peclik/ogn-airtracker/doc/img/battcharger.jpg

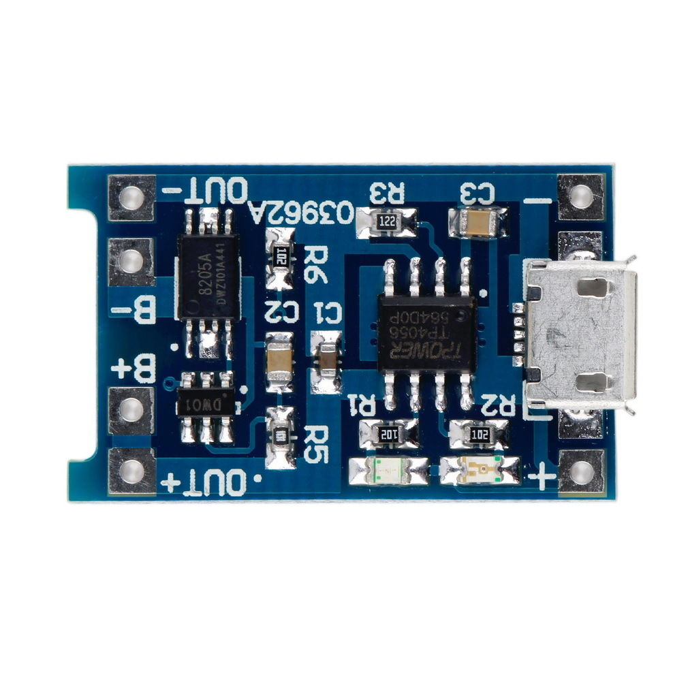
doc/img/battcharger.jpg
